DaveMelkani/geotaxis_files/Glaz_PolG_RNAi/_Output_Females/female_stats_control_Glaz_+_w3_2/female_mannwhitney_heatmap_velocity_control_Glaz_+_w3.tiff

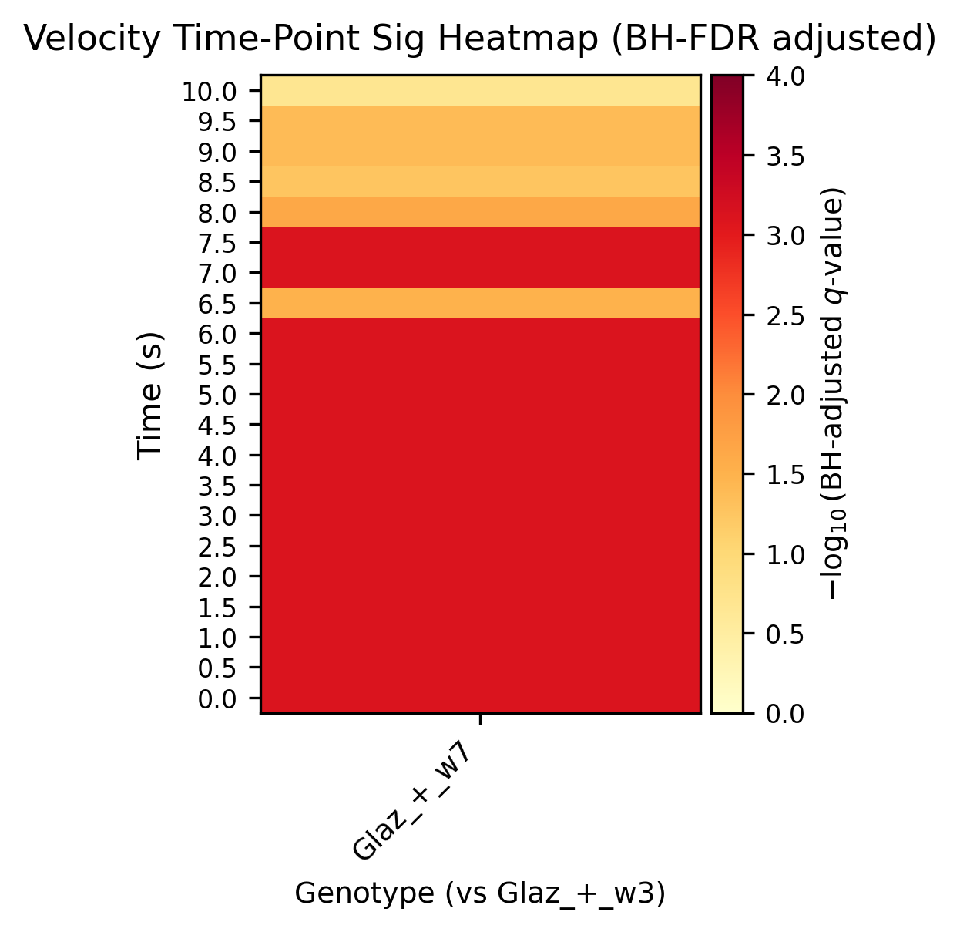
Glaz_PolG_RNAi/_Output_Females/female_stats_control_Glaz_+_w3_2/female_mannwhitney_heatmap_velocity_control_Glaz_+_w3.tiff
