DaveMelkani/geotaxis_files/Glaz_PolG_RNAi/_Output_Females/female_stats_control_Glaz_+_w7_1/female_mannwhitney_heatmap_low performer_control_Glaz_+_w7.tiff

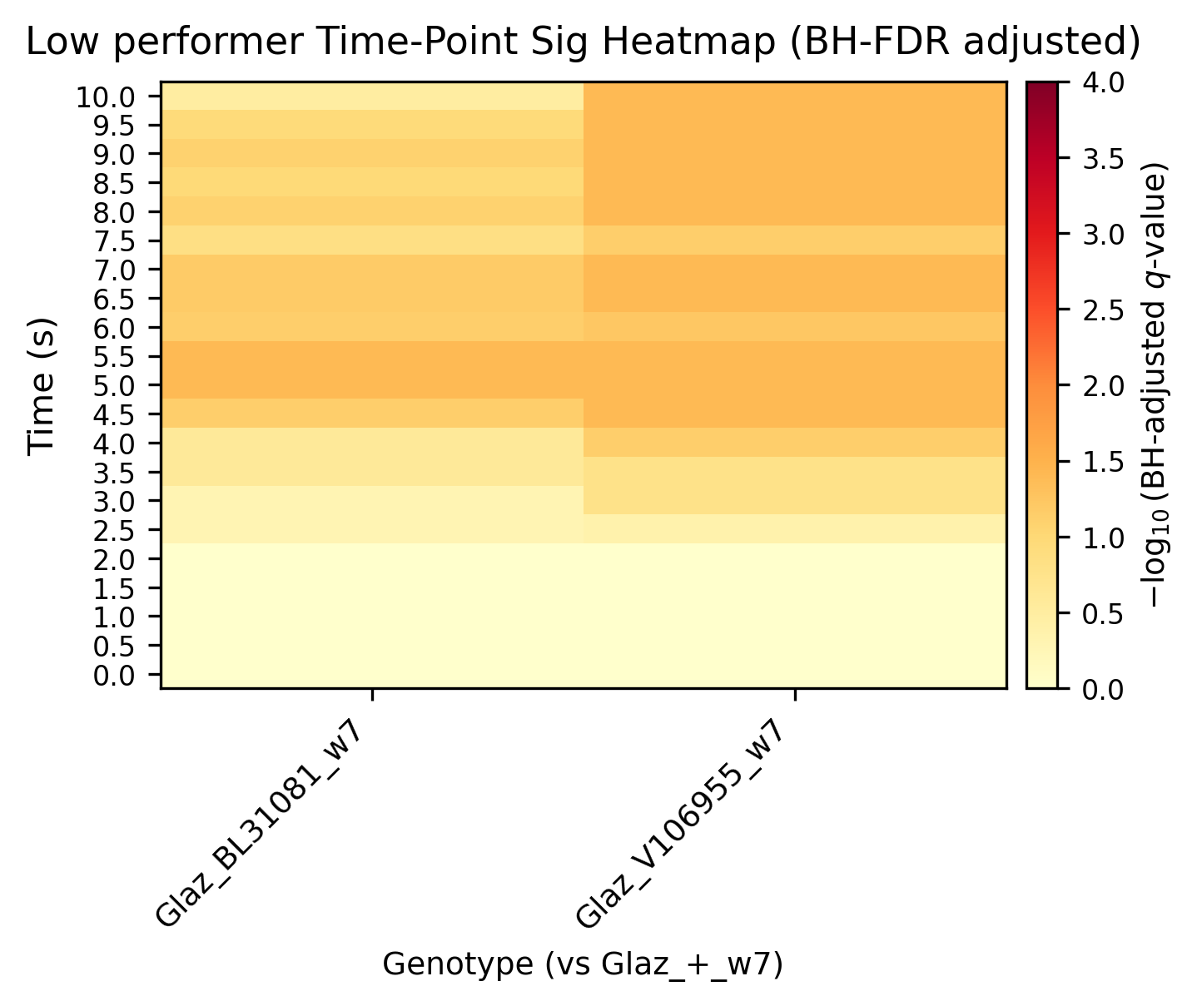
Glaz_PolG_RNAi/_Output_Females/female_stats_control_Glaz_+_w7_1/female_mannwhitney_heatmap_low performer_control_Glaz_+_w7.tiff
