DaveMelkani/geotaxis_files/Glaz_PolG_RNAi/_Output_Females/female_stats_control_Glaz_+_w7_1/female_peak_position_barplot.tiff

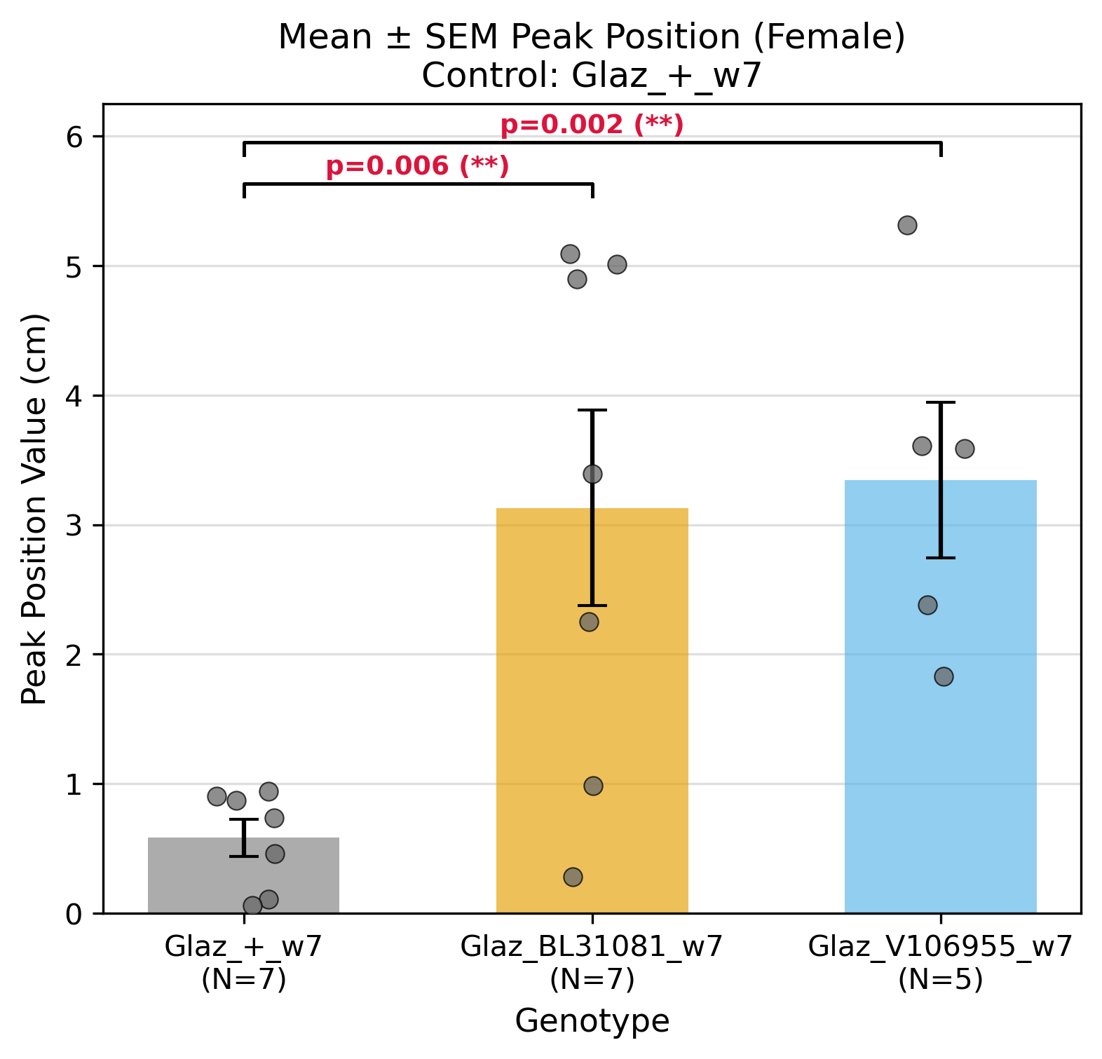
Glaz_PolG_RNAi/_Output_Females/female_stats_control_Glaz_+_w7_1/female_peak_position_barplot.tiff
