DaveMelkani/geotaxis_files/Glaz_PolG_RNAi/_Output_Females/female_stats_control_Glaz_BL31081_w3_1/female_mannwhitney_heatmap_velocity_control_Glaz_BL31081_w3.tiff

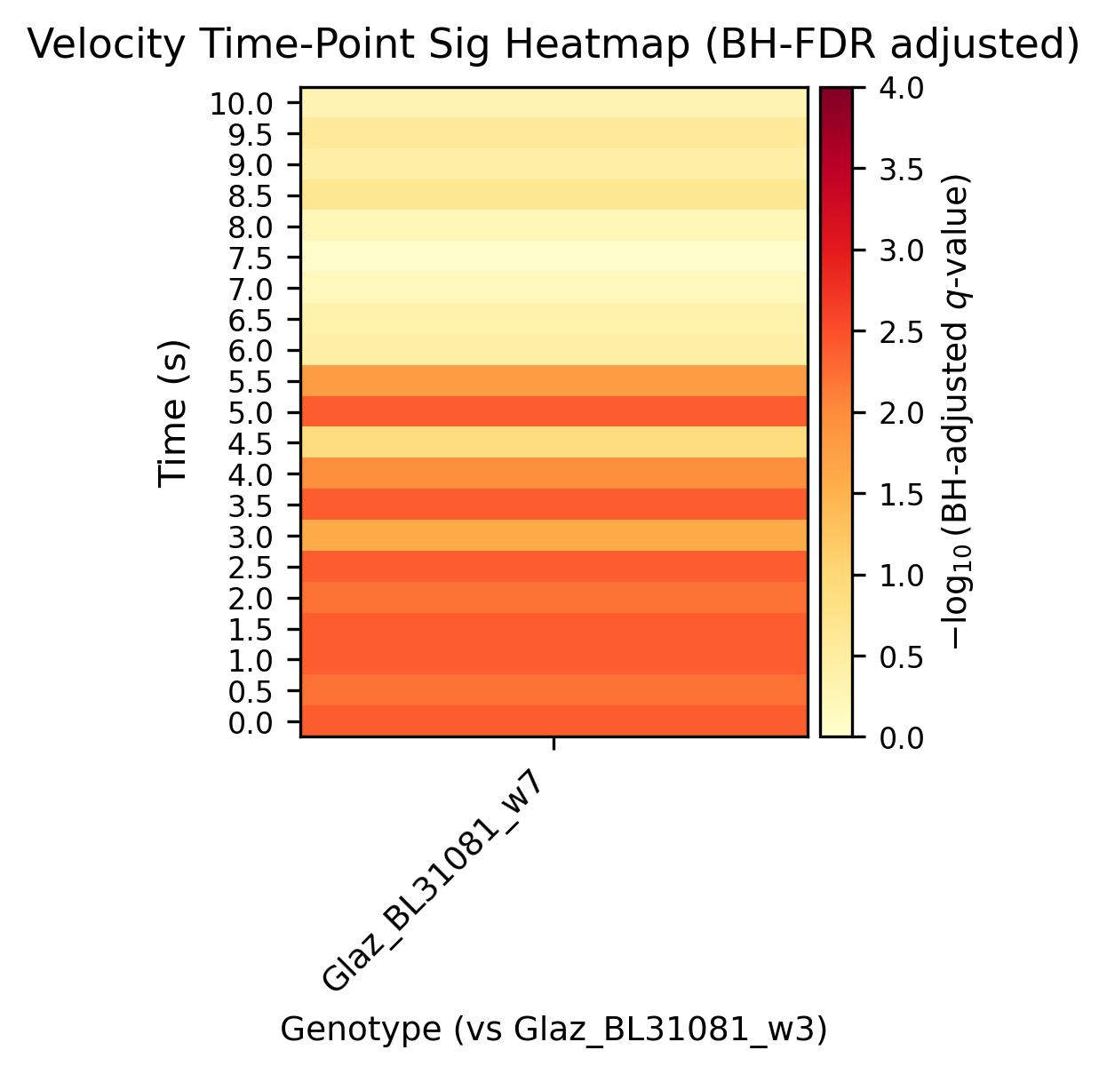
Glaz_PolG_RNAi/_Output_Females/female_stats_control_Glaz_BL31081_w3_1/female_mannwhitney_heatmap_velocity_control_Glaz_BL31081_w3.tiff
