DaveMelkani/geotaxis_files/Glaz_PolG_RNAi/_Output_Females/female_stats_control_Glaz_V106955_w3_1/female_mannwhitney_heatmap_middle performer_control_Glaz_V106955_w3.tiff

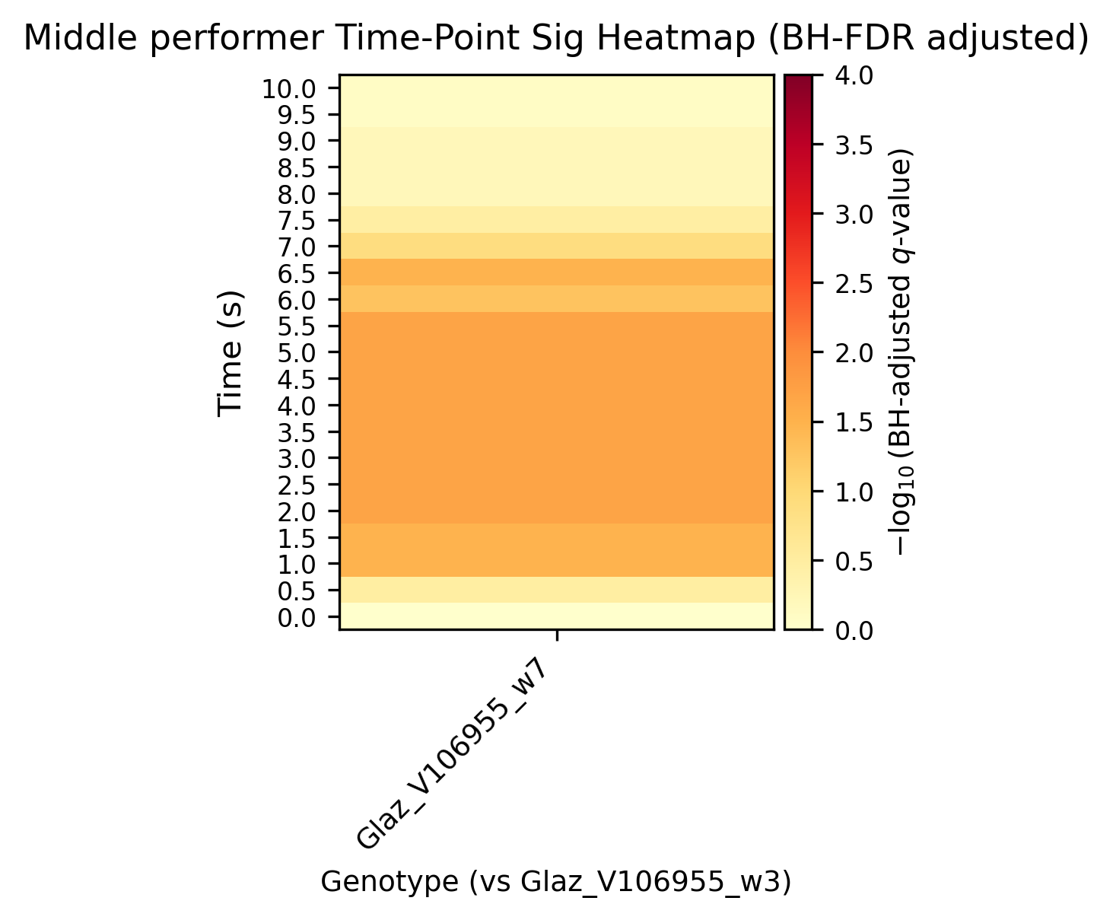
Glaz_PolG_RNAi/_Output_Females/female_stats_control_Glaz_V106955_w3_1/female_mannwhitney_heatmap_middle performer_control_Glaz_V106955_w3.tiff
