DaveMelkani/geotaxis_files/Glaz_PolG_RNAi/_Output_Males/male_stats_control_Glaz_+_w3_2/male_mannwhitney_heatmap_velocity_control_Glaz_+_w3.tiff

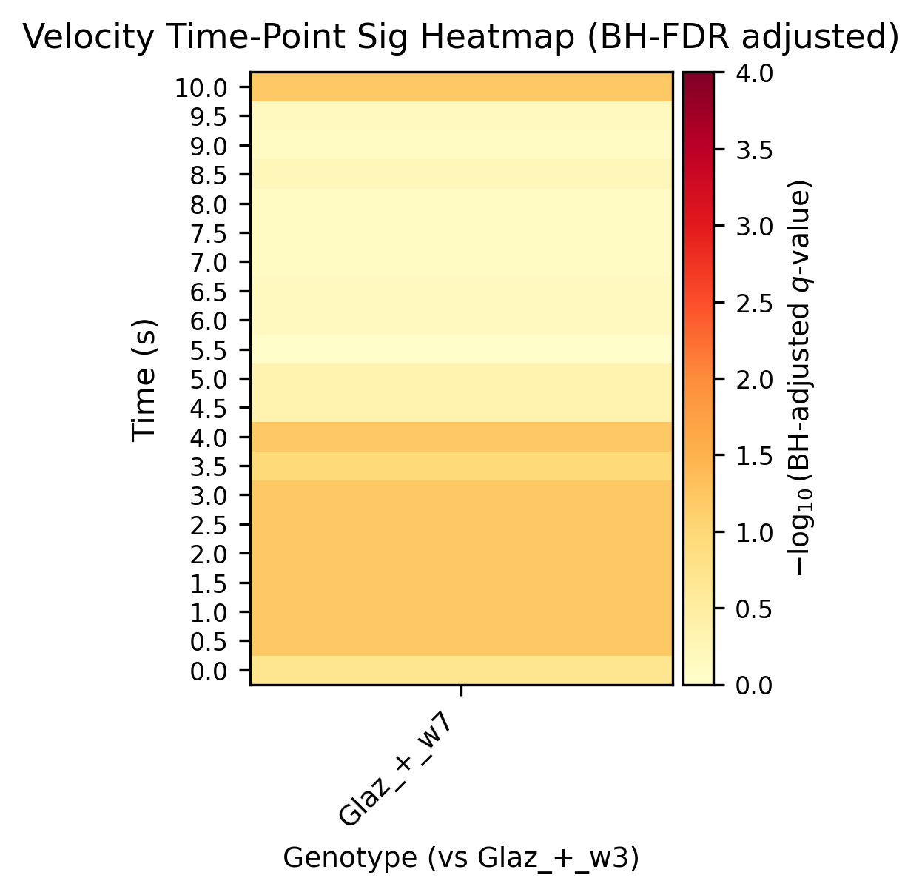
Glaz_PolG_RNAi/_Output_Males/male_stats_control_Glaz_+_w3_2/male_mannwhitney_heatmap_velocity_control_Glaz_+_w3.tiff
