DaveMelkani/geotaxis_files/Glaz_PolG_RNAi/Dev_Set1_GLAZ_PLOG1_3wk_Jan_13_2025/percentage_MP_plot.png

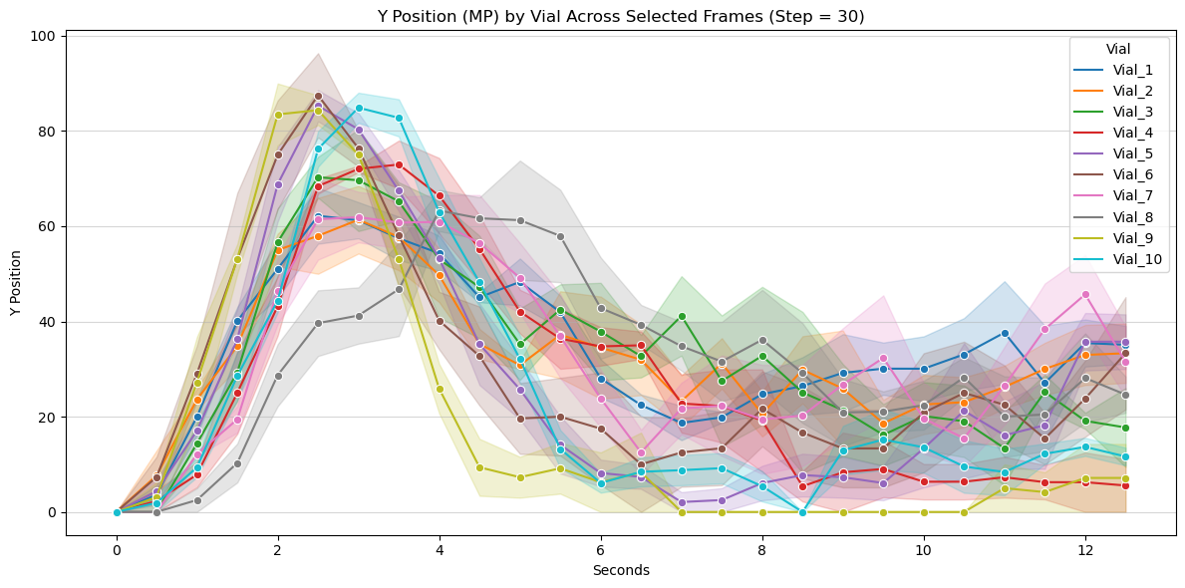
Glaz_PolG_RNAi/Dev_Set1_GLAZ_PLOG1_3wk_Jan_13_2025/percentage_MP_plot.png
