DaveMelkani/geotaxis_files/Glaz_PolG_RNAi/Dev_Set1_GLAZ_POLG1_3wk_Jan_27_2025/position_Total_plot.png

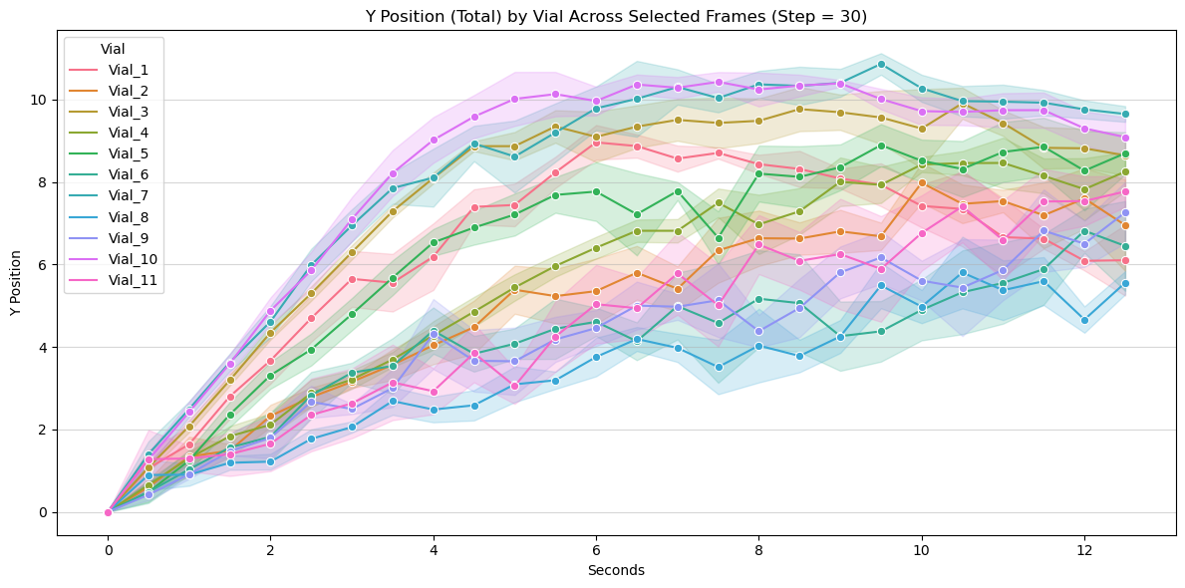
Glaz_PolG_RNAi/Dev_Set1_GLAZ_POLG1_3wk_Jan_27_2025/position_Total_plot.png
