DaveMelkani/geotaxis_files/Glaz_PolG_RNAi/Dev_Set1_GLAZ_POLG1_3wk_May_06_2025/position_Total_plot.png

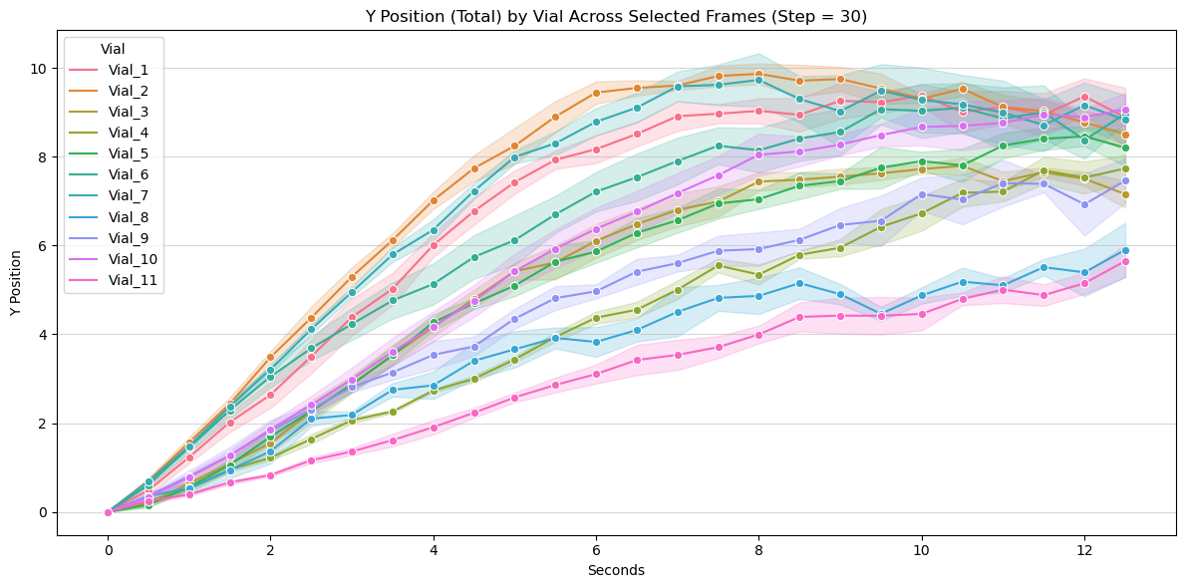
Glaz_PolG_RNAi/Dev_Set1_GLAZ_POLG1_3wk_May_06_2025/position_Total_plot.png
