DaveMelkani/geotaxis_files/Glaz_PolG_RNAi/Dev_Set2_GLAZ_PLOG1_3wk_Jan_13_2025/percentage_LP_plot.png

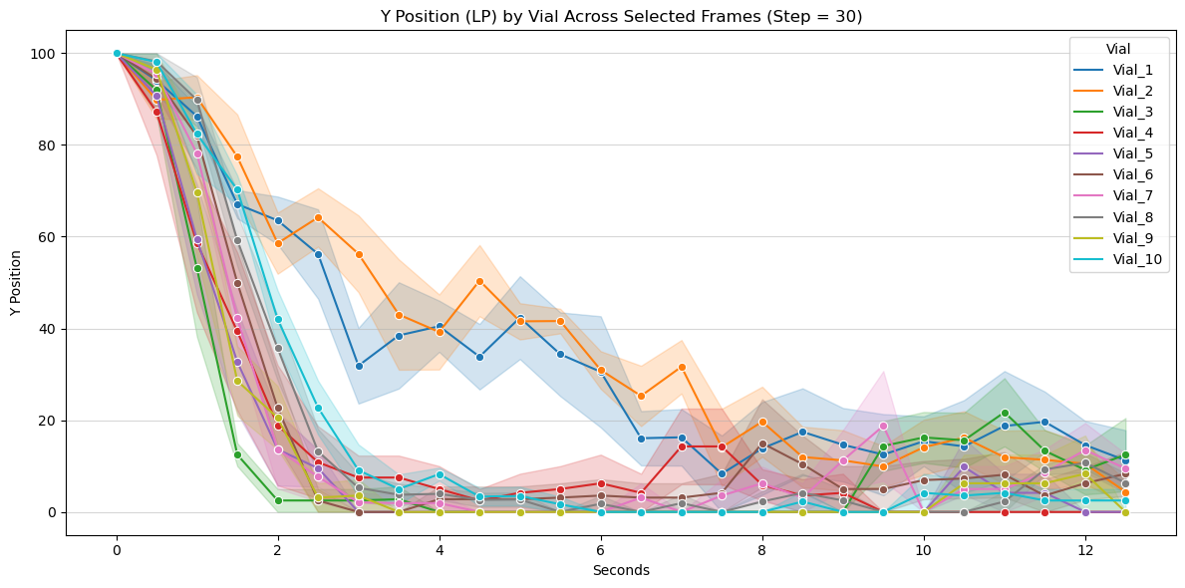
Glaz_PolG_RNAi/Dev_Set2_GLAZ_PLOG1_3wk_Jan_13_2025/percentage_LP_plot.png
