DaveMelkani/geotaxis_files/Glaz_PolG_RNAi/Dev_Set2_GLAZ_POLG1_3wk_Jan_27_2024/percentage_MP_plot.png

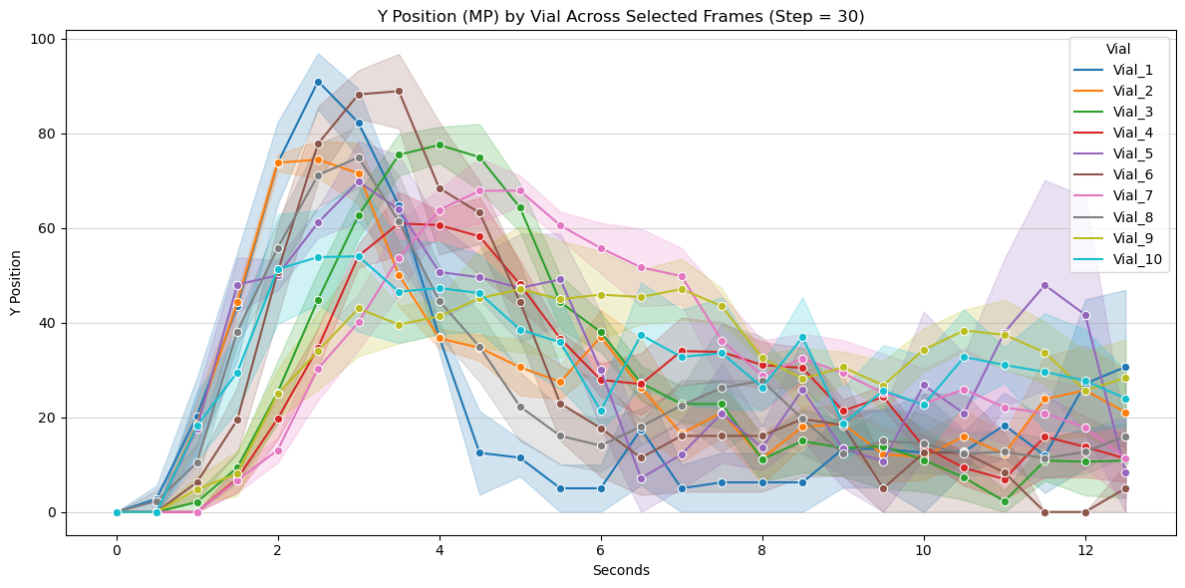
Glaz_PolG_RNAi/Dev_Set2_GLAZ_POLG1_3wk_Jan_27_2024/percentage_MP_plot.png
