DaveMelkani/geotaxis_files/Glaz_PolG_RNAi/Dev_Set2_GLAZ_POLG1_3wk_May_06_2025/percentage_LP_plot.png

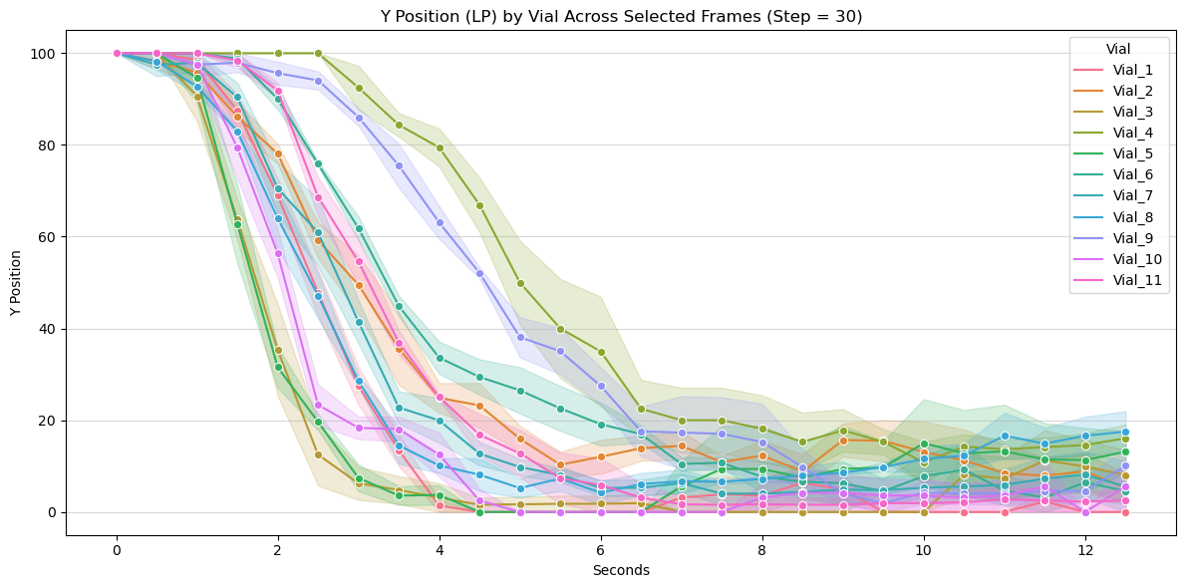
Glaz_PolG_RNAi/Dev_Set2_GLAZ_POLG1_3wk_May_06_2025/percentage_LP_plot.png
