DaveMelkani/geotaxis_files/Glaz_PolG_RNAi/Dev_Set2_GLAZ_POLG1_7wk_Feb_20_2025/percentage_HP_plot.png

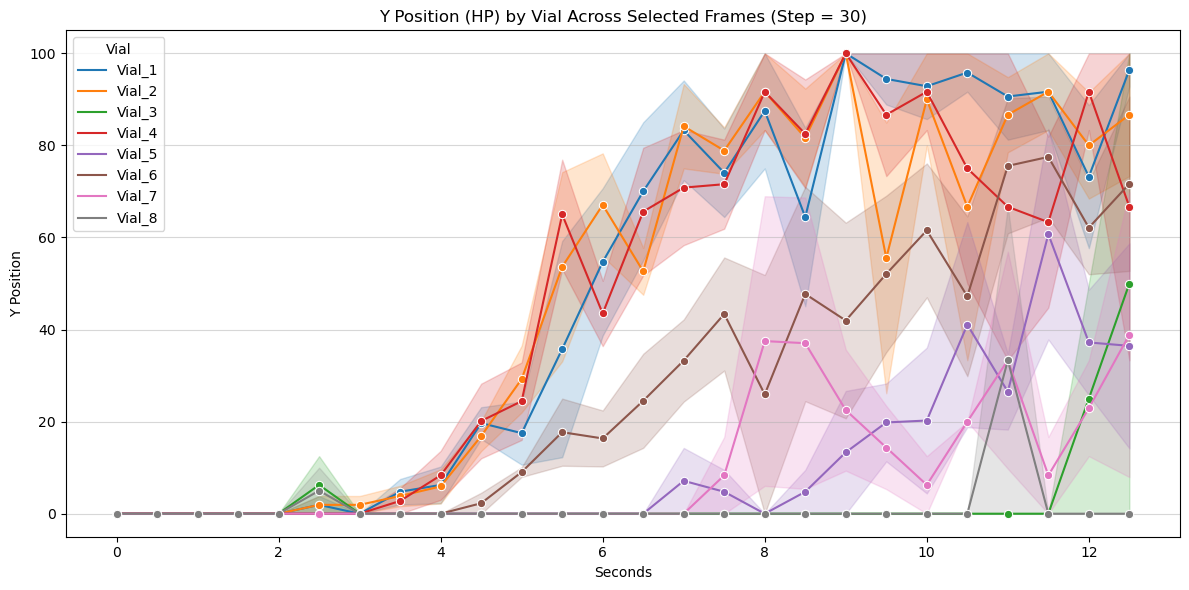
Glaz_PolG_RNAi/Dev_Set2_GLAZ_POLG1_7wk_Feb_20_2025/percentage_HP_plot.png
