DaveMelkani/geotaxis_files/Glaz_PolG_RNAi/Dev_Set3_GLAZ_POLG1_7wk_Feb_12_2025/percentage_LP_plot.png

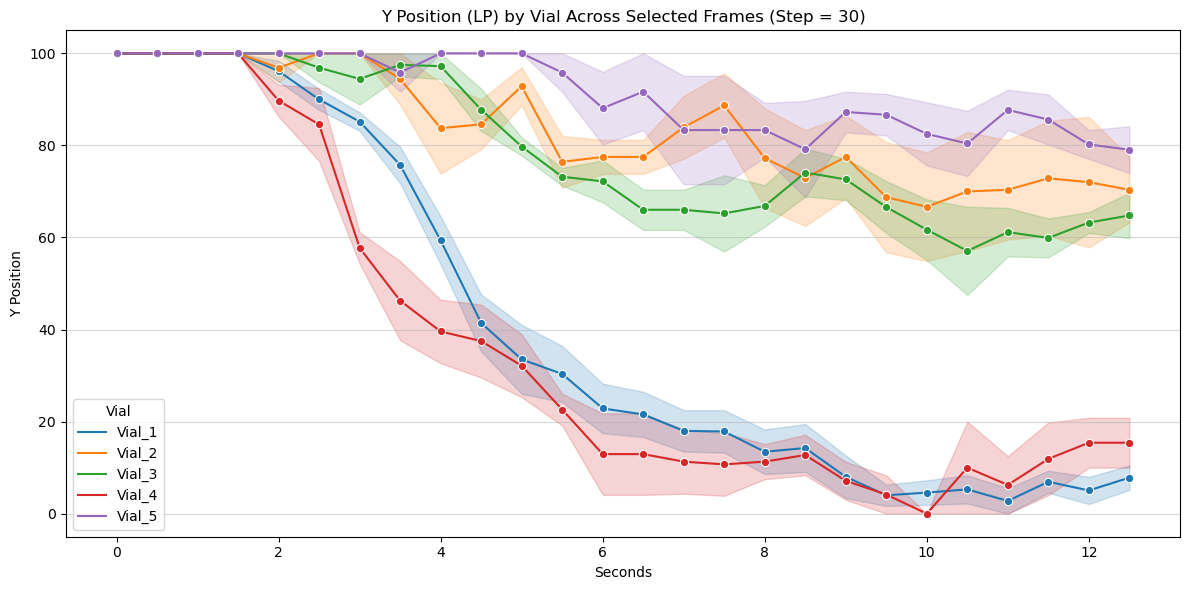
Glaz_PolG_RNAi/Dev_Set3_GLAZ_POLG1_7wk_Feb_12_2025/percentage_LP_plot.png
