DaveMelkani/geotaxis_files/Glaz_PolG_RNAi/Dev_Set3_GLAZ_POLG1_7wk_June_03_2025/percentage_HP_plot.png

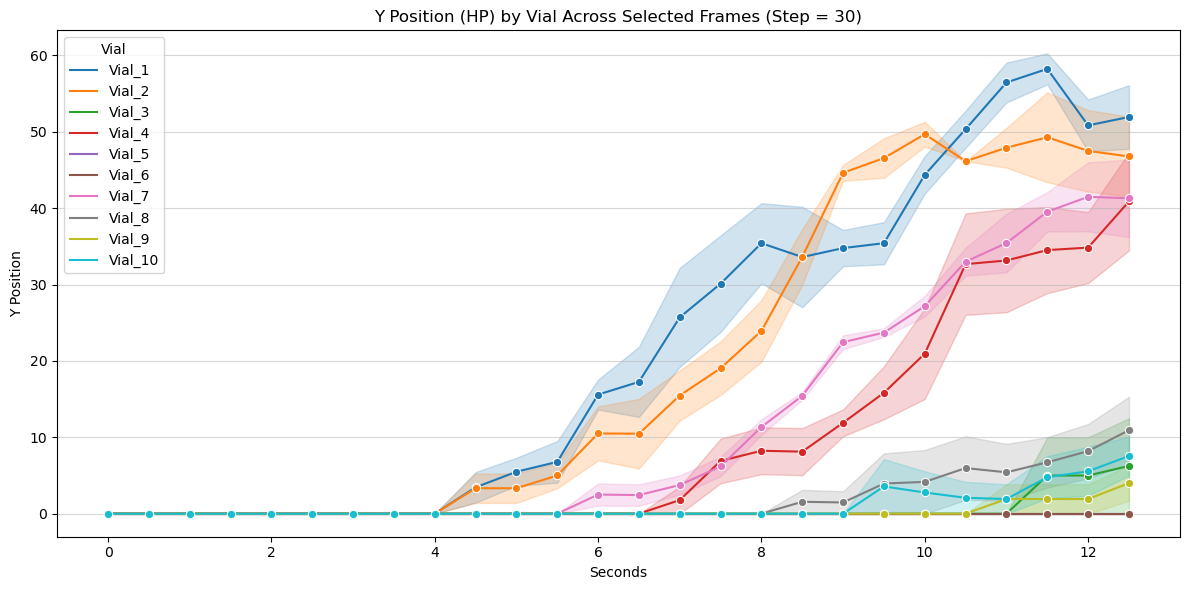
Glaz_PolG_RNAi/Dev_Set3_GLAZ_POLG1_7wk_June_03_2025/percentage_HP_plot.png
