DaveMelkani/geotaxis_files/Glaz_PolG_RNAi/Dev_Set4_GLAZ_POLG1_7wk_June_03_2025/percentage_MP_plot.png

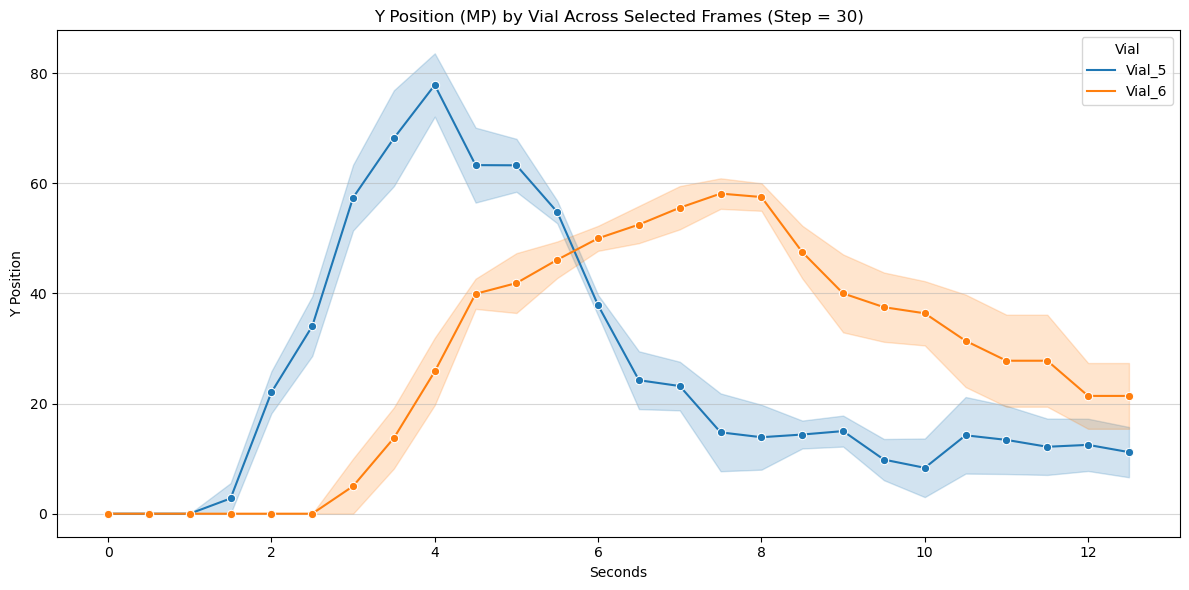
Glaz_PolG_RNAi/Dev_Set4_GLAZ_POLG1_7wk_June_03_2025/percentage_MP_plot.png
