DaveMelkani/geotaxis_files/W1118_CLKOut/_Output_Females/female_stats_control_CLK_Out_w1_1/female_mannwhitney_heatmap_high performer_control_CLK_Out_w1.tiff

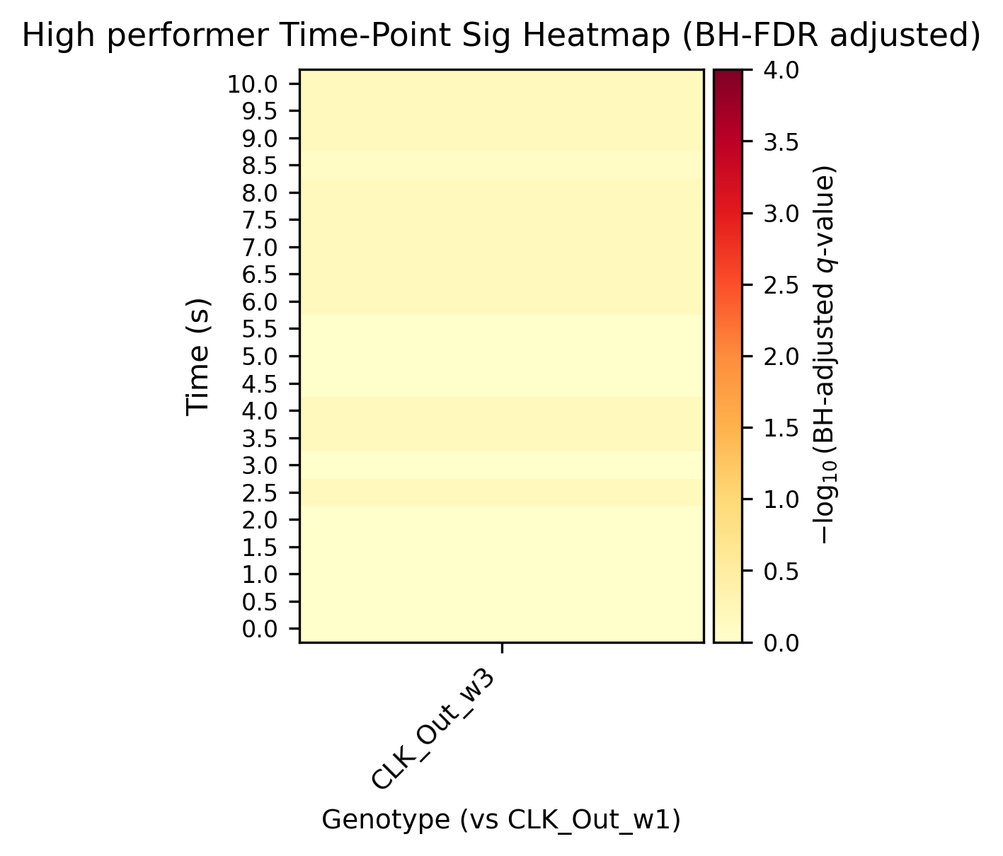
W1118_CLKOut/_Output_Females/female_stats_control_CLK_Out_w1_1/female_mannwhitney_heatmap_high performer_control_CLK_Out_w1.tiff
