DaveMelkani/geotaxis_files/W1118_CLKOut/_Output_Females/female_stats_control_CLK_Out_w1_1/female_peak_position_barplot.tiff

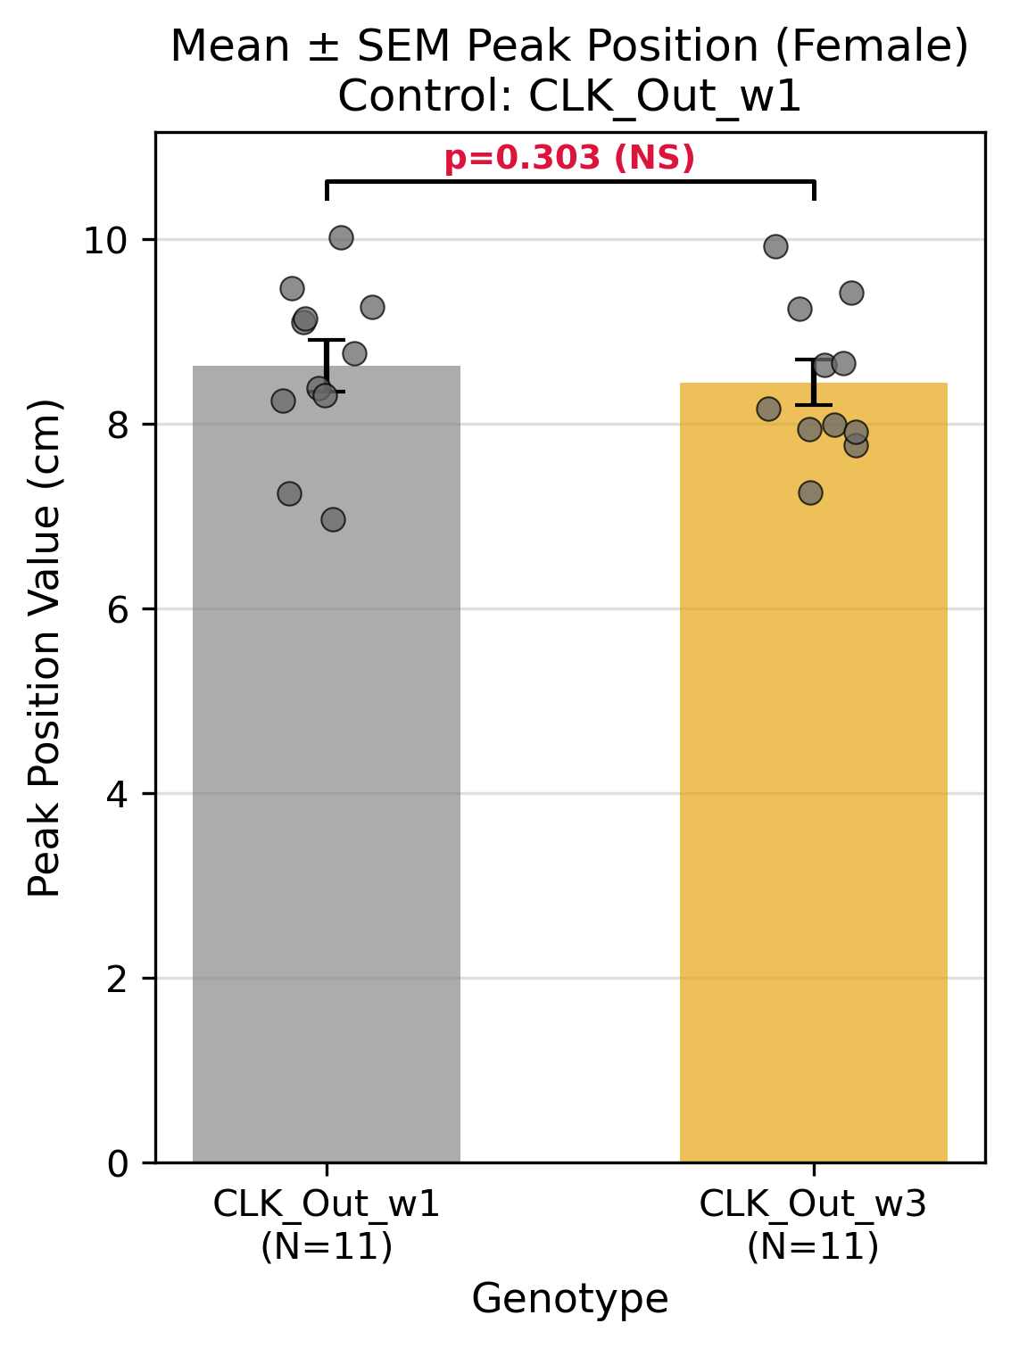
W1118_CLKOut/_Output_Females/female_stats_control_CLK_Out_w1_1/female_peak_position_barplot.tiff
