DaveMelkani/geotaxis_files/W1118_CLKOut/_Output_Females/female_stats_control_W1118_w1_2/female_mannwhitney_heatmap_position_control_W1118_w1.tiff

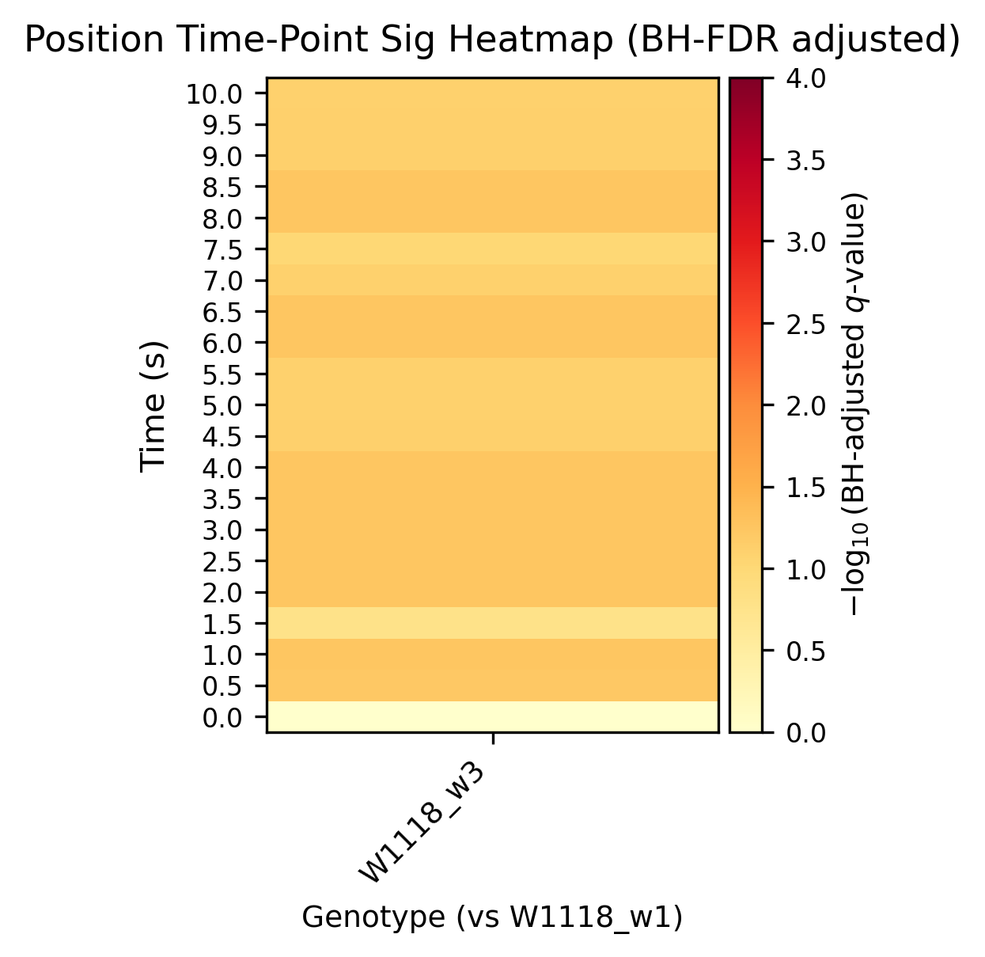
W1118_CLKOut/_Output_Females/female_stats_control_W1118_w1_2/female_mannwhitney_heatmap_position_control_W1118_w1.tiff
