DaveMelkani/geotaxis_files/W1118_CLKOut/_Output_Females/female_stats_control_W1118_w3_1/female_peak_position_barplot.tiff

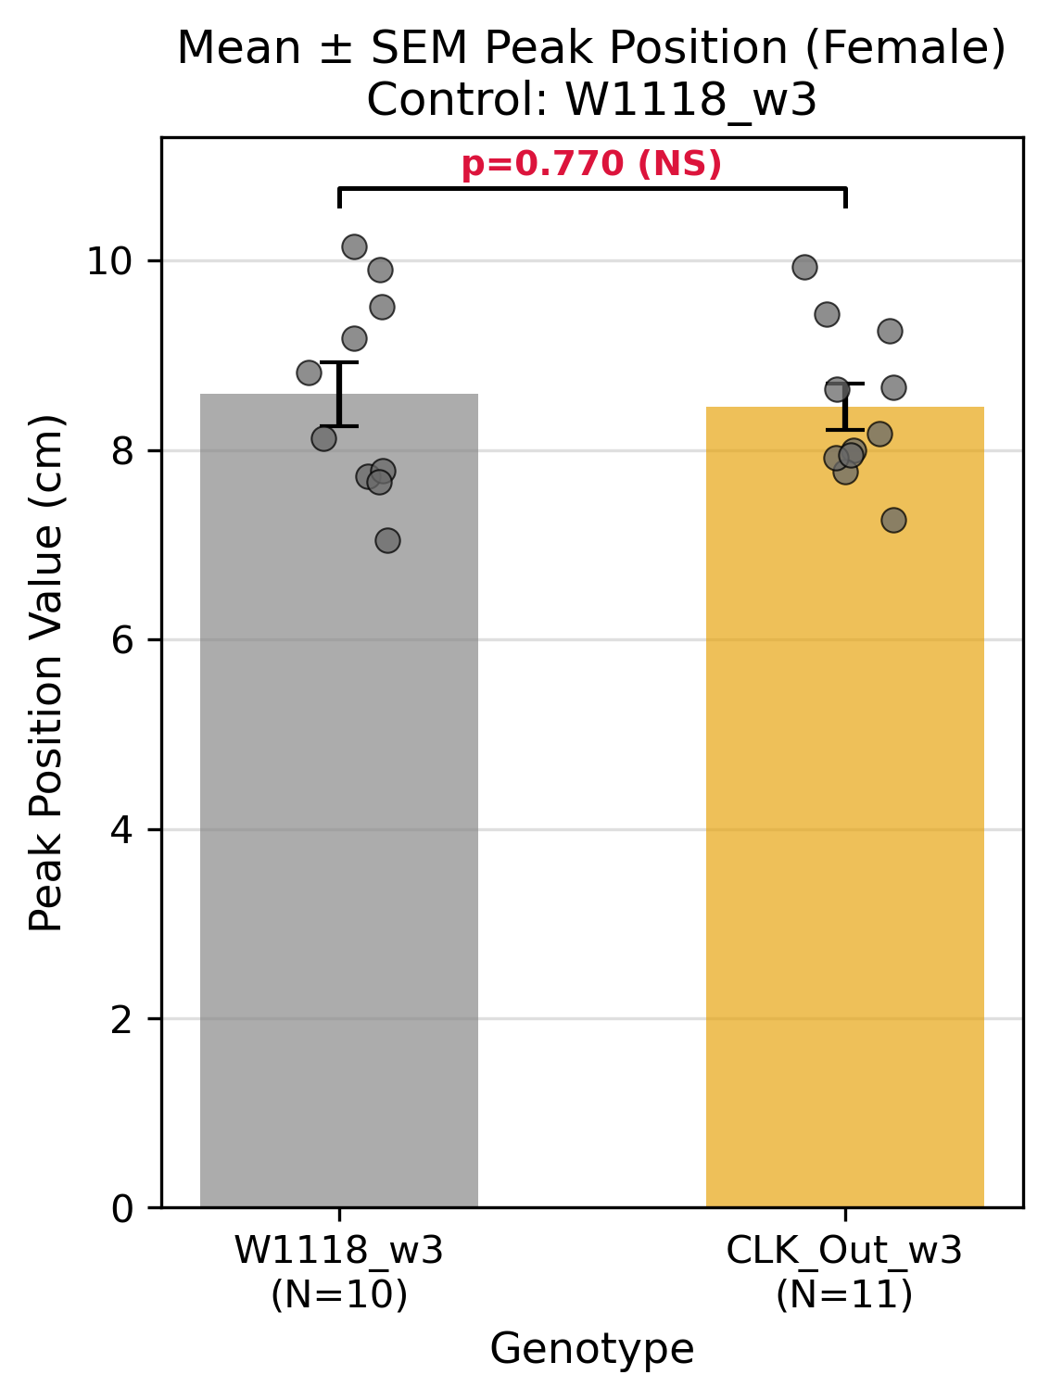
W1118_CLKOut/_Output_Females/female_stats_control_W1118_w3_1/female_peak_position_barplot.tiff
