DaveMelkani/geotaxis_files/W1118_CLKOut/_Output_Males/male_stats_control_W1118_w1_1/male_mannwhitney_heatmap_high performer_control_W1118_w1.tiff

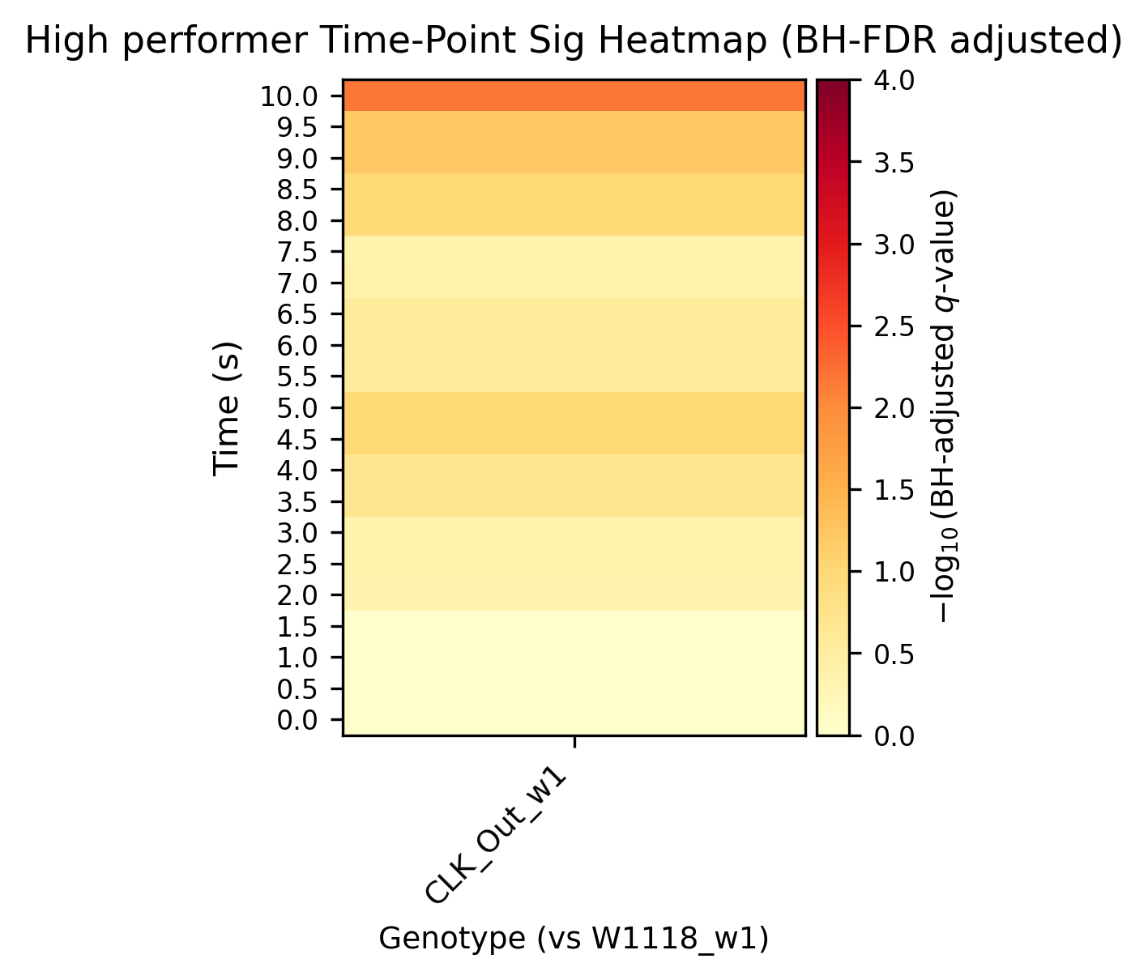
W1118_CLKOut/_Output_Males/male_stats_control_W1118_w1_1/male_mannwhitney_heatmap_high performer_control_W1118_w1.tiff
