DaveMelkani/geotaxis_files/W1118_CLKOut/_Output_Males/male_stats_control_W1118_w1_1/male_peak_position_barplot.tiff

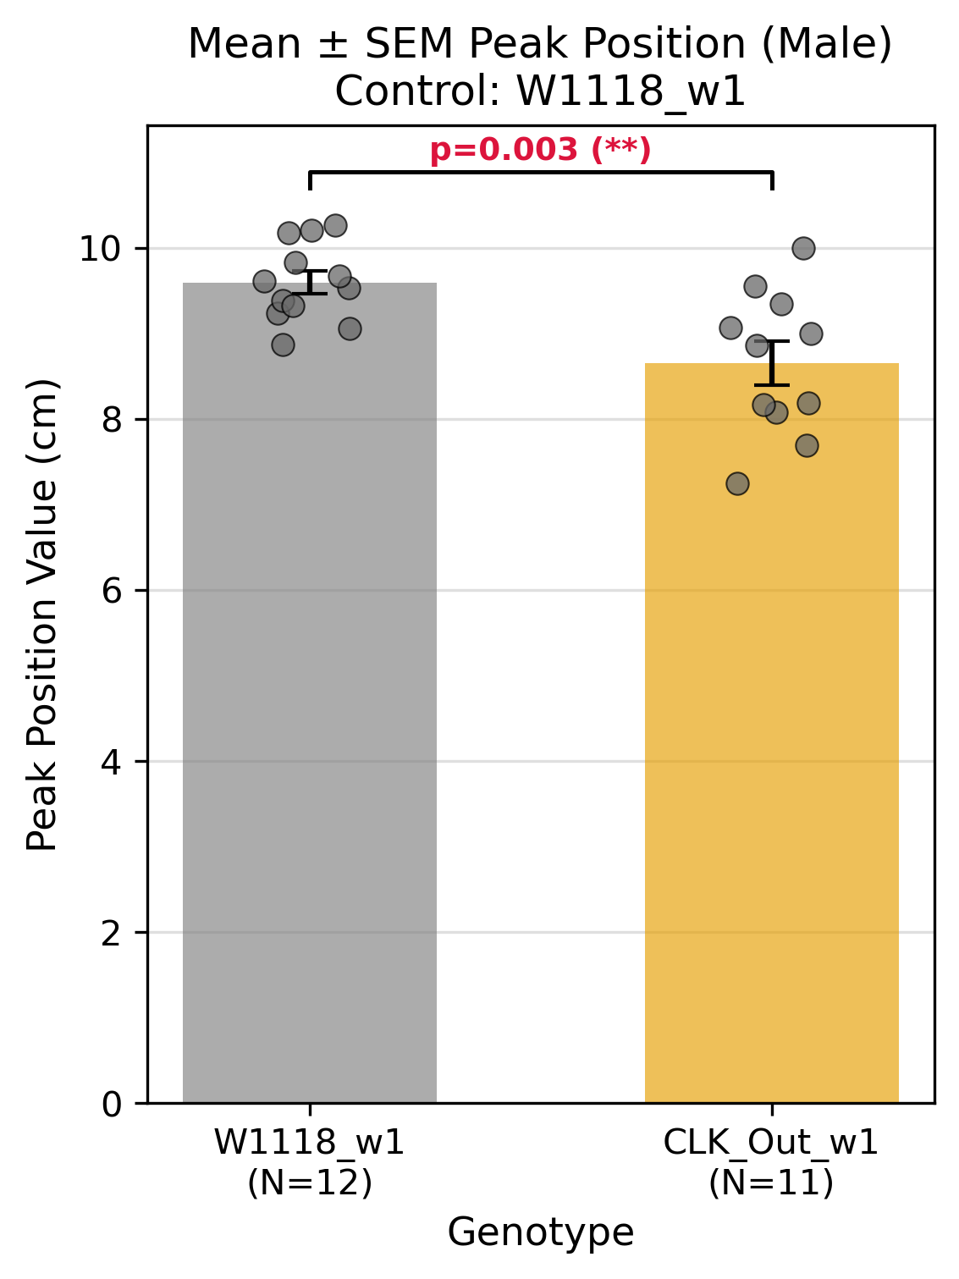
W1118_CLKOut/_Output_Males/male_stats_control_W1118_w1_1/male_peak_position_barplot.tiff
