DaveMelkani/geotaxis_files/main_stl_files_and_folders/1_curved_vial_holder/Curved_TopCover.stl

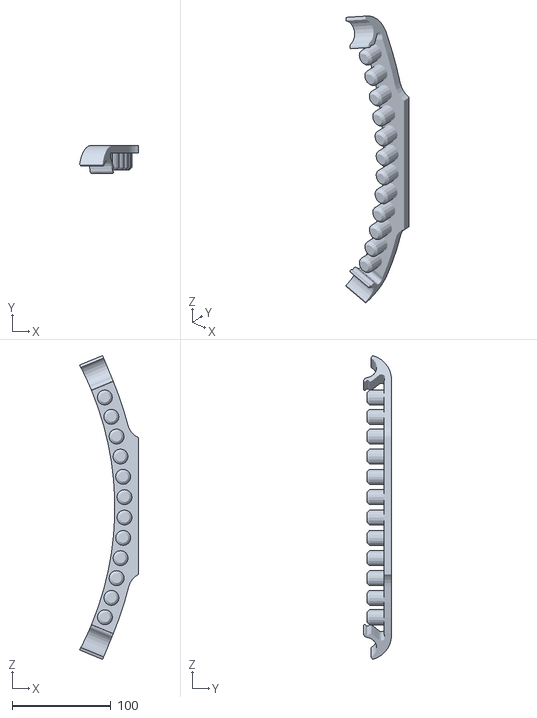
[picture p125: CAD file, 2026-05-21]
main_stl_files_and_folders/1_curved_vial_holder/Curved_TopCover.stl
59.7 x 28.1 x 308.2
