DaveMelkani/geotaxis_files/main_stl_files_and_folders/2_middle_parts_attach_holder_pivot_fulcrum/Piston_Push_Mid-link.stl

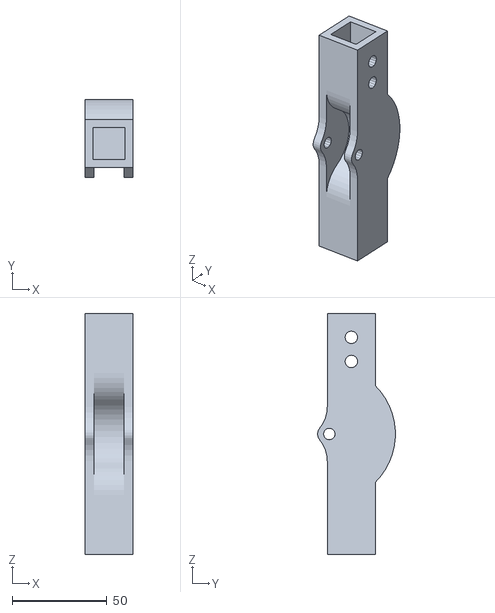
[picture p126: CAD file, 2026-05-21]
main_stl_files_and_folders/2_middle_parts_attach_holder_pivot_fulcrum/Piston_Push_Mid-link.stl
25.4 x 40.9 x 127.0
