DaveMelkani/geotaxis_files/main_stl_files_and_folders/3_connecting_rod/Top_Push_Cylinder.stl

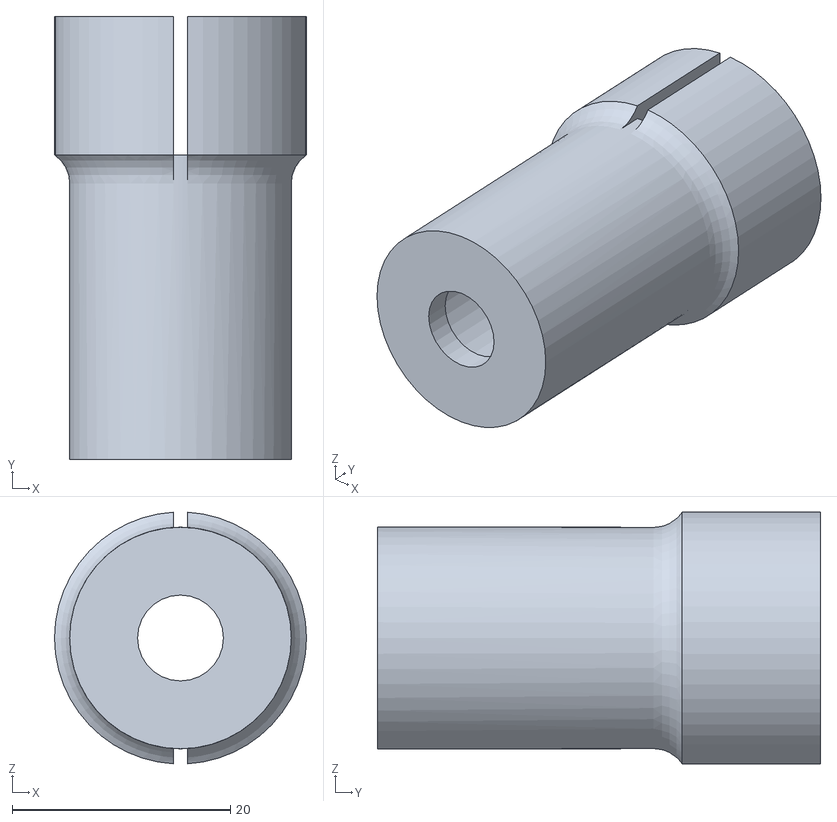
[picture p127: CAD file, 2026-05-21]
main_stl_files_and_folders/3_connecting_rod/Top_Push_Cylinder.stl
23.1 x 40.6 x 23.1
