DaveMelkani/geotaxis_files/main_stl_files_and_folders/4_crank_input_link/Crank_Hand.stl

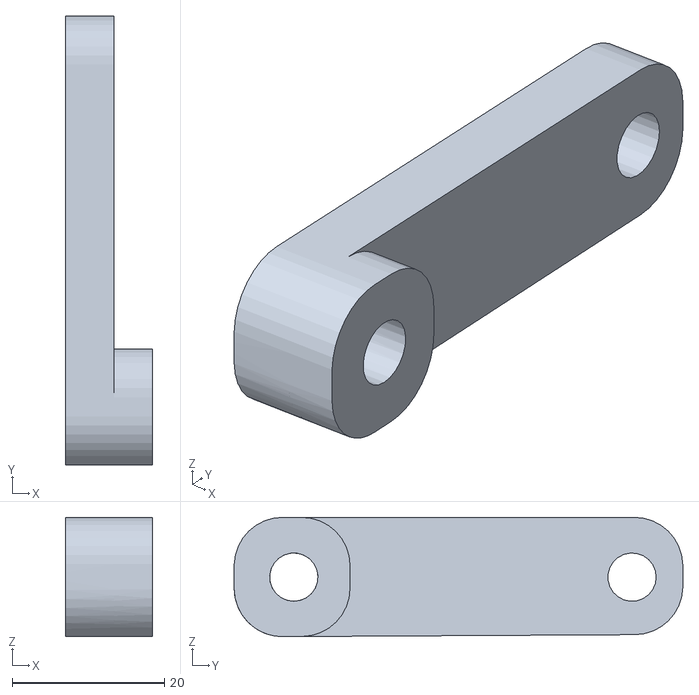
[picture p128: CAD file, 2026-05-21]
main_stl_files_and_folders/4_crank_input_link/Crank_Hand.stl
11.4 x 59.0 x 15.7
