DaveMelkani/geotaxis_files/main_stl_files_and_folders/5_motor_drive/Motor_Brace.stl

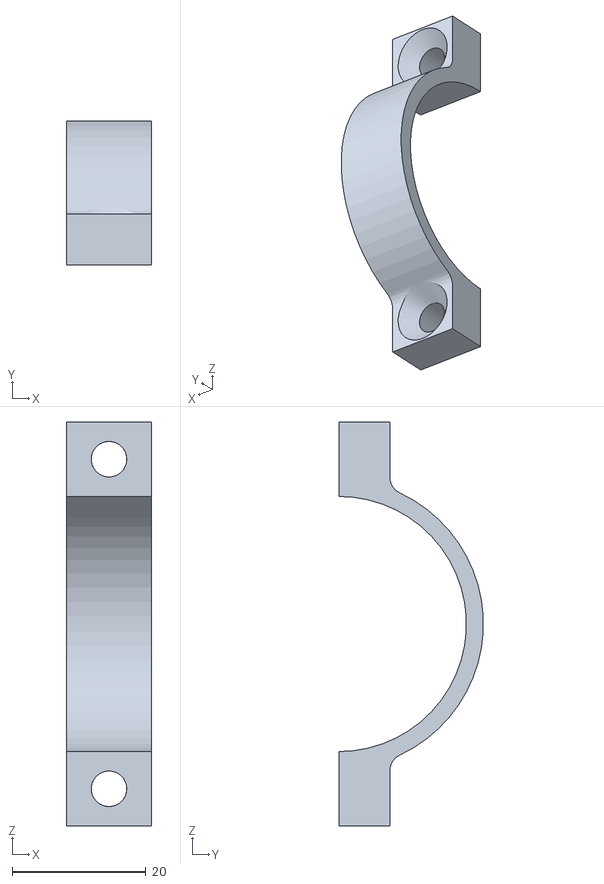
[picture p129: CAD file, 2026-05-21]
main_stl_files_and_folders/5_motor_drive/Motor_Brace.stl
12.7 x 21.6 x 60.3
