DaveMelkani/geotaxis_files/main_stl_files_and_folders/2_middle_parts_attach_holder_pivot_fulcrum/Vial_Holder_Connector.stl

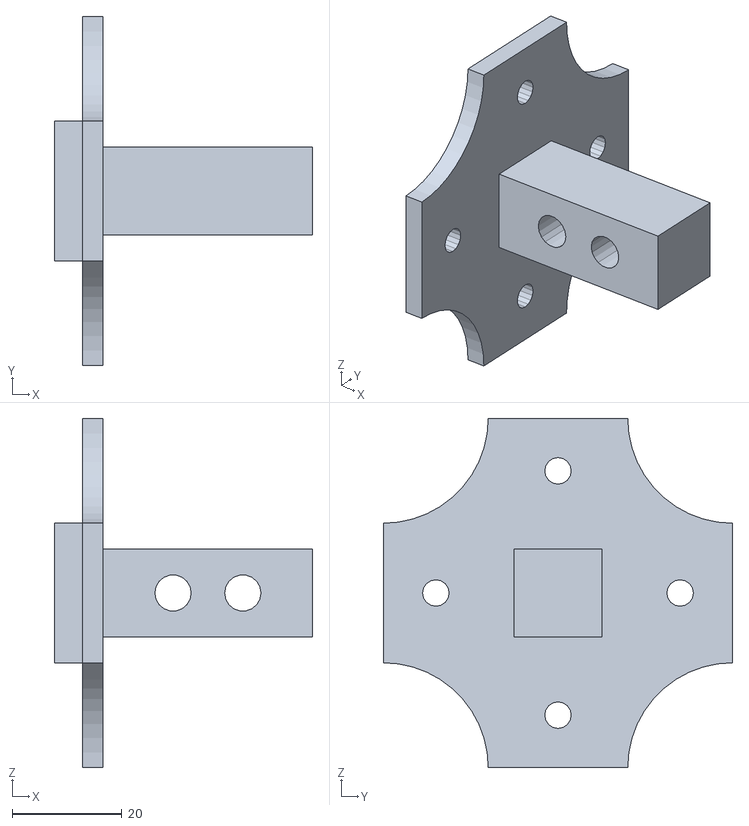
[picture p130: CAD file, 2026-05-21]
main_stl_files_and_folders/2_middle_parts_attach_holder_pivot_fulcrum/Vial_Holder_Connector.stl
47.0 x 63.5 x 63.5
