DaveMelkani/geotaxis_files/main_stl_files_and_folders/5_motor_drive/Big_Motor_Faceplate.stl

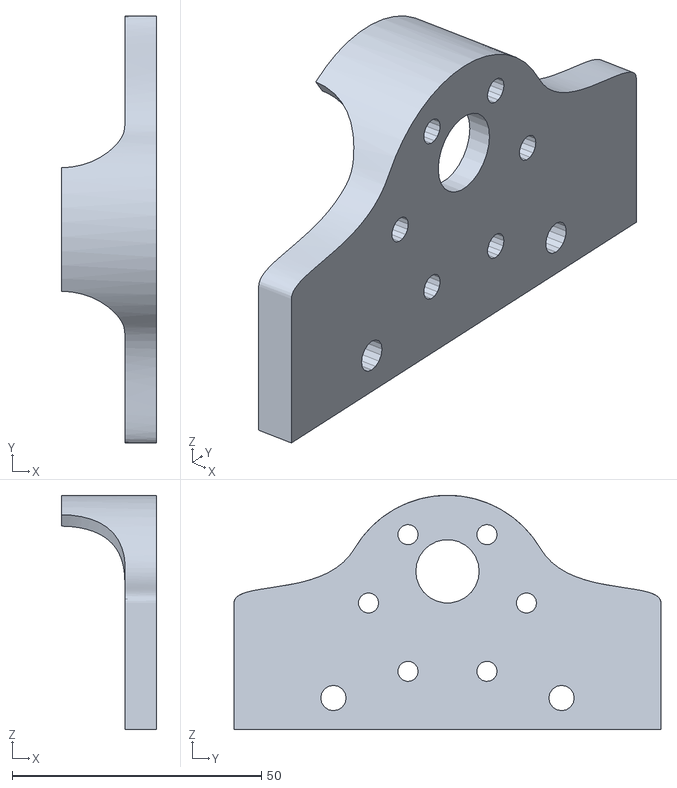
[picture p131: CAD file, 2026-05-21]
main_stl_files_and_folders/5_motor_drive/Big_Motor_Faceplate.stl
19.1 x 85.6 x 47.0
