DaveMelkani/geotaxis_files/main_stl_files_and_folders/2_middle_parts_attach_holder_pivot_fulcrum/Arm_Length_Body.stl

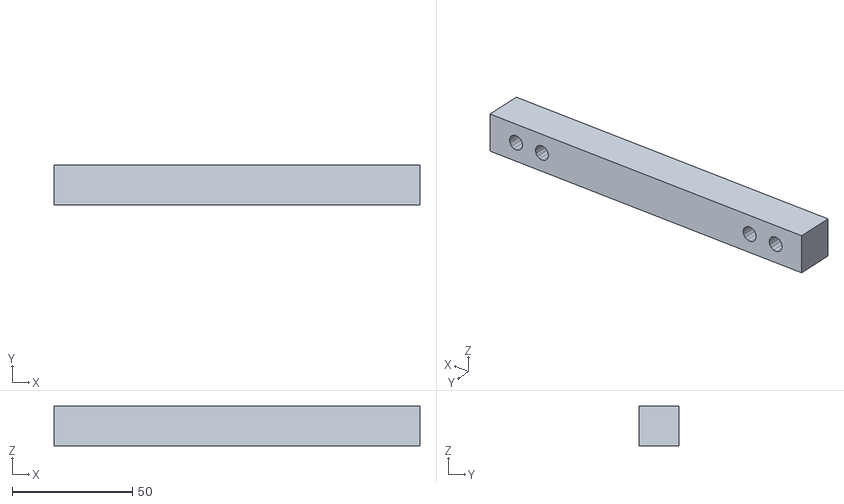
[picture p132: CAD file, 2026-05-21]
main_stl_files_and_folders/2_middle_parts_attach_holder_pivot_fulcrum/Arm_Length_Body.stl
152.4 x 16.5 x 16.5
