DaveMelkani/geotaxis_files/main_stl_files_and_folders/5_motor_drive/GeoT_gear_crank.stl

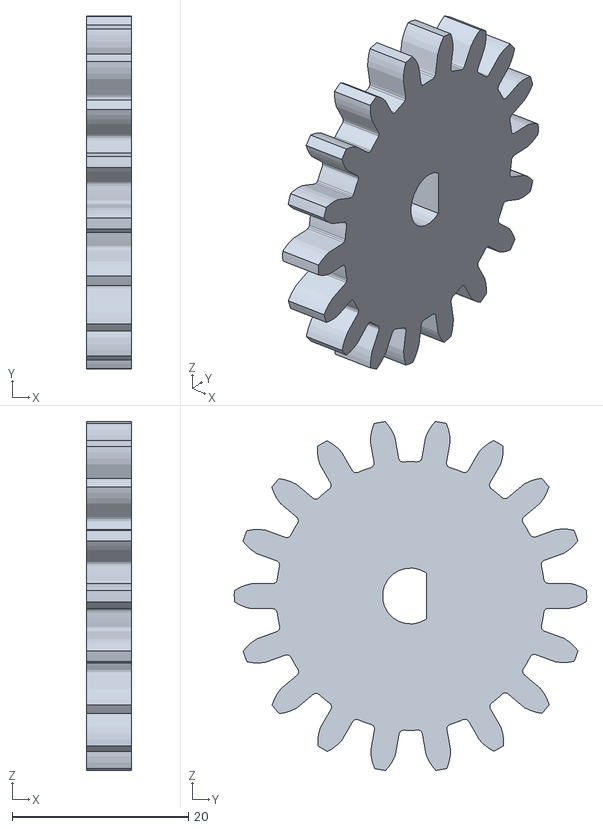
[picture p133: CAD file, 2026-05-21]
main_stl_files_and_folders/5_motor_drive/GeoT_gear_crank.stl
5.08 x 40.0 x 39.6
